MATTMCCA/The-Black-Hellebore/src/ProjectPics/img001.jpeg

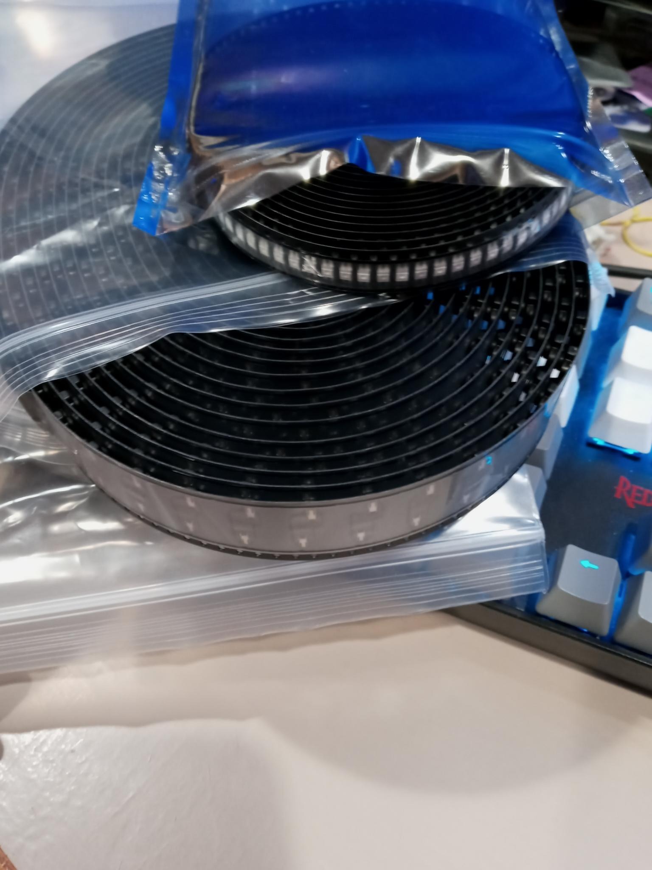
src/ProjectPics/img001.jpeg
