MATTMCCA/The-Black-Hellebore/src/ProjectPics/img002.jpeg

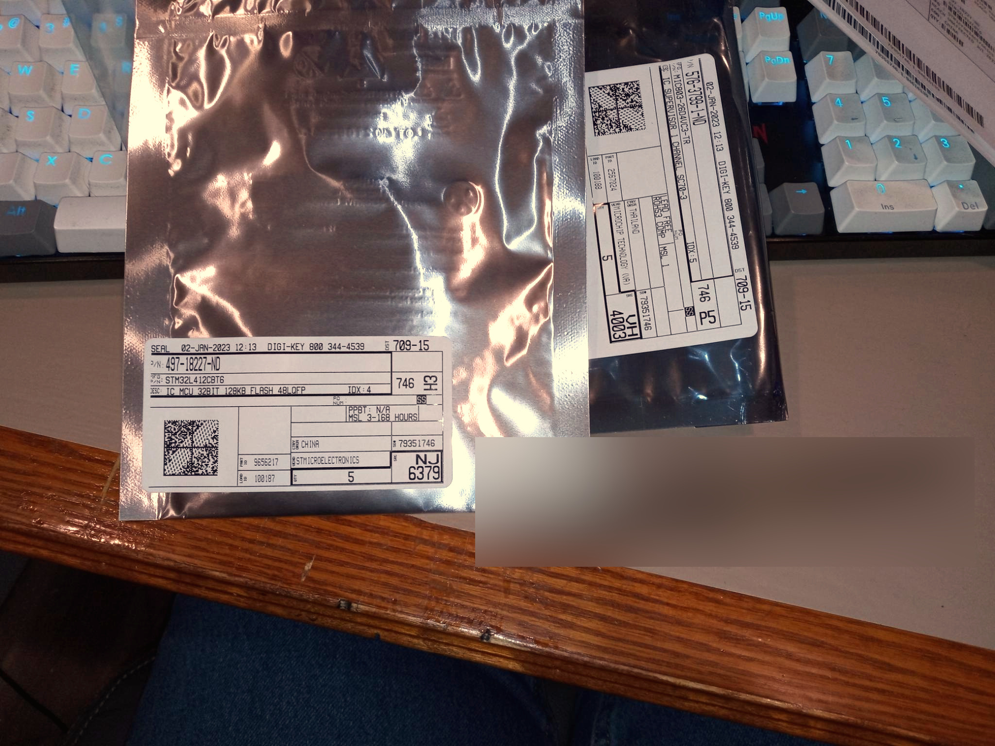
src/ProjectPics/img002.jpeg
