MATTMCCA/The-Black-Hellebore/src/ProjectPics/img004.jpeg

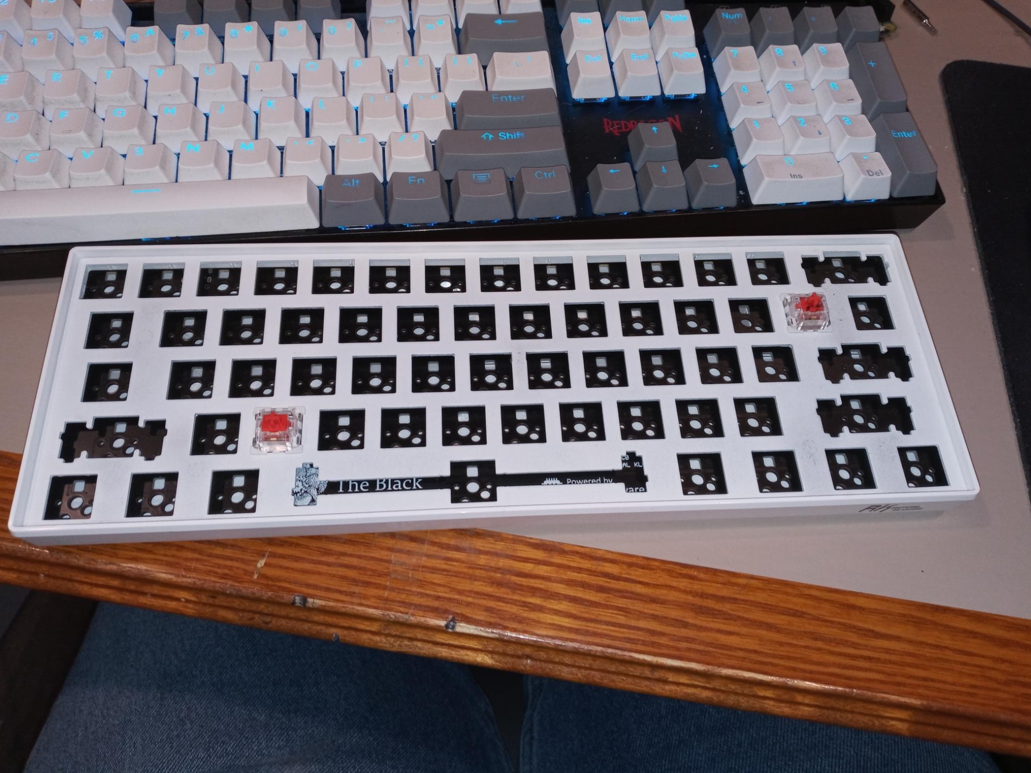
src/ProjectPics/img004.jpeg
