MATTMCCA/The-Black-Hellebore/src/ProjectPics/img005.jpeg

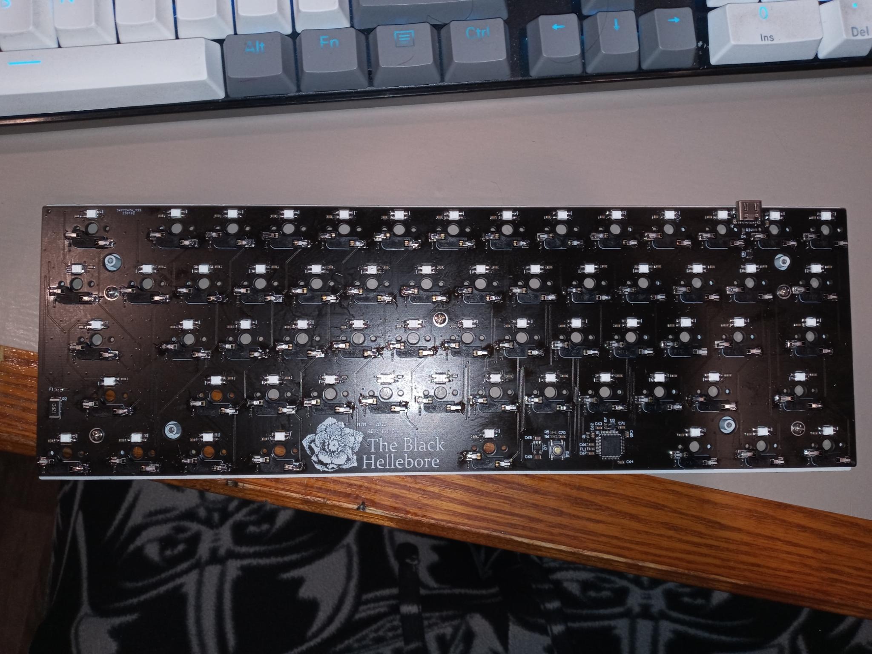
src/ProjectPics/img005.jpeg
