MATTMCCA/The-Black-Hellebore/src/ProjectPics/img006.jpeg

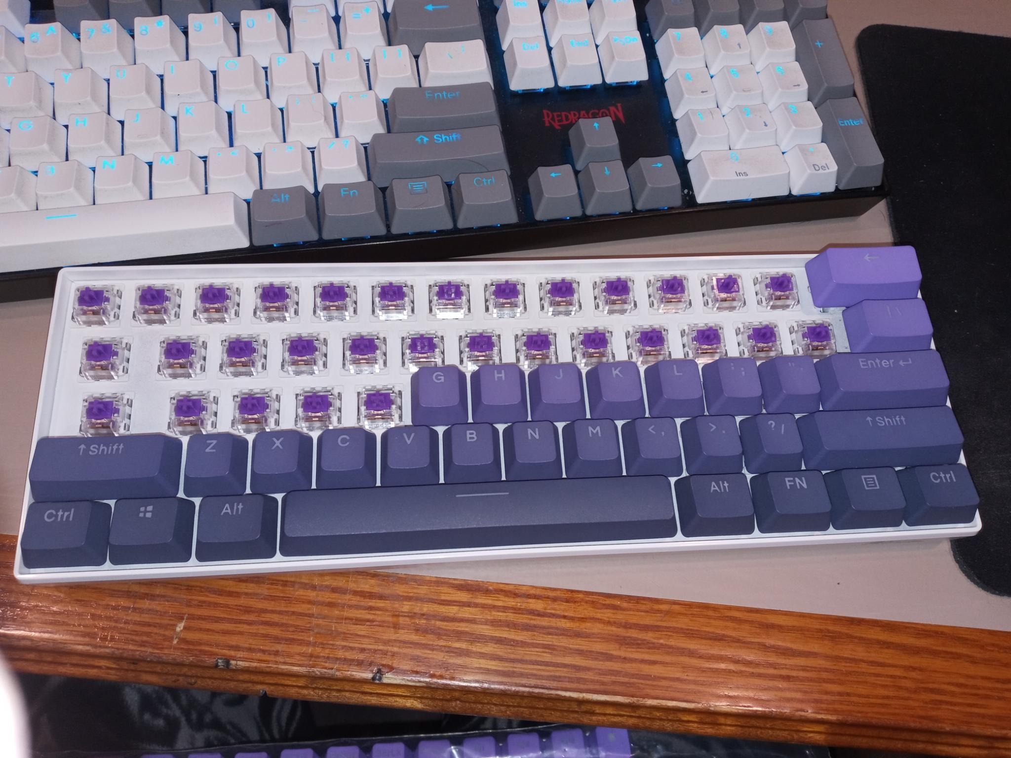
src/ProjectPics/img006.jpeg
