MATTMCCA/The-Black-Hellebore/src/ProjectPics/img007.jpeg

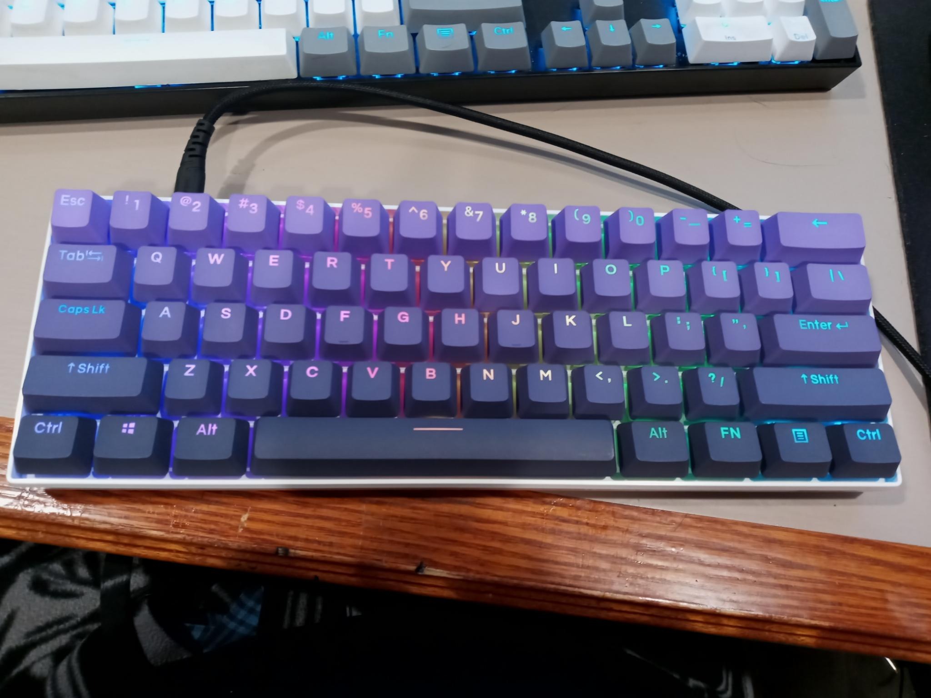
src/ProjectPics/img007.jpeg
