MATTMCCA/The-Black-Hellebore/src/ProjectPics/img008.jpeg

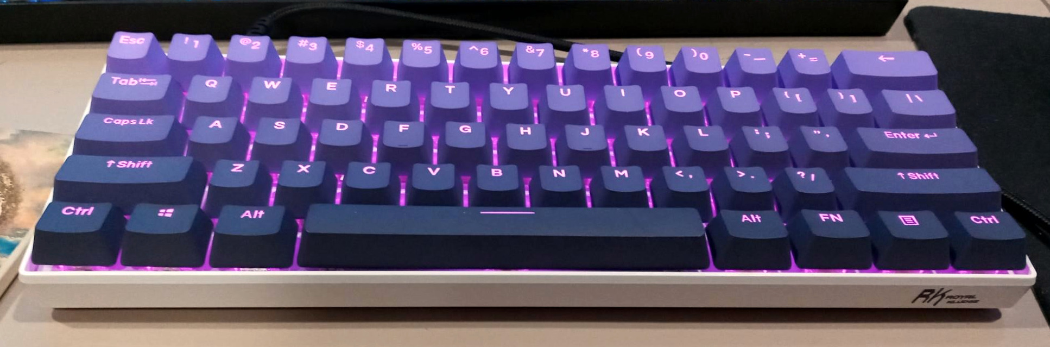
src/ProjectPics/img008.jpeg
